MitchellStride/Hello-My-Name-Is-PCB-Badge/hello_my_name_is/sim/usb_pwr_sel.asc

C1: cap; 1µ
C2: cap
D1: schottky; 1N5819
M2: pmos; ""
R1: res; 10k
R2: res; 1k
R4: res; 10
V1: voltage; 3.3
V2: voltage; 5
V3: voltage; PULSE(0 5 100m 0 0 50m 100m)
Named nets: 3V3, 0, 5V, 5V_PULSE, 3V3_HS
.include C:\\Users\\mitch\\projects\\badge\\hello_my_name_is\\hello_my_name_is\\sim\\AO3401.mod
.tran 1
