MitchellStride/Hello-My-Name-Is-PCB-Badge/hello_my_name_is/sim/slide_sw.asc

C1: cap; 1µ
M1: nmos; ""
R1: res; 1k
R2: res; 10k
R4: res; 10
V1: voltage; 3.3
V2: voltage; 5
V3: voltage; PULSE(0 3.3 100m 0 0 50m 100m)
Named nets: BATT_GND, 3V3, 0, 5V, 3V3_PULSE
.include C:\\Users\\mitch\\projects\\badge\\hello_my_name_is\\hello_my_name_is\\sim\\AO3400.mod
.tran 1
