MitchellStride/Hello-My-Name-Is-PCB-Badge/hello_my_name_is/software/unit_tests/oled.py

# https://pypi.org/project/oled-text/

# Display Image & text on I2C driven ssd1306 OLED display
from machine import Pin, I2C
from ssd1306 import SSD1306_I2C
import utime
import framebuf

#N096-2864KSWEG01-H30
WIDTH = 128 # oled display width
HEIGHT = 64 # oled display height

oled_rst = machine.Pin(15, machine.Pin.OUT)
oled_rst.low()
utime.sleep(0.1)
oled_rst.high()
i2c = machine.I2C(0, sda=machine.Pin(16), scl=machine.Pin(17))

#i2c = I2C(0) # Init I2C using I2C0 defaults,
#SCL=Pin(GP9), SDA=Pin(GP8), freq=400000
print("I2C Address : "+hex(i2c.scan()[0]).upper()) # Display device address
print("I2C Configuration: "+str(i2c)) # Display I2C config

oled = SSD1306_I2C(WIDTH, HEIGHT, i2c) # Init oled display

# Raspberry Pi logo as 32x32 bytearray
buffer = bytearray(b"\x00\x00\x00\x00\x00\x00\x00\x00\x00\x00\x00\x00\x00|?\x00\x01\x86@\x80\x01\x01\x80\x80\x01\x11\x88\x80\x01\x05\xa0\x80\x00\x83\xc1\x00\x00C\xe3\x00\x00~\xfc\x00\x00L'\x00\x00\x9c\x11\x00\x00\xbf\xfd\x00\x00\xe1\x87\x00\x01\xc1\x83\x80\x02A\x82@\x02A\x82@\x02\xc1\xc2@\x02\xf6>\xc0\x01\xfc=\x80\x01\x18\x18\x80\x01\x88\x10\x80\x00\x8c!\x00\x00\x87\xf1\x00\x00\x7f\xf6\x00\x008\x1c\x00\x00\x0c \x00\x00\x03\xc0\x00\x00\x00\x00\x00\x00\x00\x00\x00\x00\x00\x00\x00")

buffer2 = bytearray(b'0xff, 0xff, 0xff, 0xff, 0xff, 0xff, 0xff, 0xff, 0xff, 0xff, 0xff, 0xff, 0xff, 0xff, 0xff, 0xff
0xff, 0xff, 0xff, 0xff, 0xff, 0xff, 0xff, 0xff, 0xff, 0xff, 0xff, 0xff, 0xff, 0xff, 0xff, 0xff
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
oled.fill(0)

# Blit the image from the framebuffer to the oled display
oled.blit(fb, 96, 0)

# Add some text
oled.text("Raspberry Pi",5,5)
oled.text("Pico",5,15)
oled.text("#badgelife", 25, 35)
oled.text("Mitch Stride", 15, 55)

# Finally update
oled.show()
