MitchellStride/Hello-My-Name-Is-PCB-Badge/hello_my_name_is/software/unit_tests/button_irq.py

import machine
import utime

button_SW4_UP = machine.Pin(0, machine.Pin.IN)
button_SW5_DOWN = machine.Pin(1, machine.Pin.IN) 

button_SW4_UP.irq(lambda pin: print("IRQ with flags:", pin.irq().flags()), machine.Pin.IRQ_FALLING)
